kiu/lightdesk/firmware/desk-light-ctl2/desk-light-ctl2/src/tc16.c

/**
 * \file
 *
 * \brief TC16 related functionality implementation.
 (c) 2020 Microchip Technology Inc. and its subsidiaries.

    Subject to your compliance with these terms,you may use this software and
    any derivatives exclusively with Microchip products.It is your responsibility
    to comply with third party license terms applicable to your use of third party
    software (including open source software) that may accompany Microchip software.

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
    IN NO EVENT WILL MICROCHIP BE LIABLE FOR ANY INDIRECT, SPECIAL, PUNITIVE,
    INCIDENTAL OR CONSEQUENTIAL LOSS, DAMAGE, COST OR EXPENSE OF ANY KIND
    WHATSOEVER RELATED TO THE SOFTWARE, HOWEVER CAUSED, EVEN IF MICROCHIP HAS
    BEEN ADVISED OF THE POSSIBILITY OR THE DAMAGES ARE FORESEEABLE. TO THE
    FULLEST EXTENT ALLOWED BY LAW, MICROCHIP'S TOTAL LIABILITY ON ALL CLAIMS IN
    ANY WAY RELATED TO THIS SOFTWARE WILL NOT EXCEED THE AMOUNT OF FEES, IF ANY,
    THAT YOU HAVE PAID DIRECTLY TO MICROCHIP FOR THIS SOFTWARE.
 */

/**
 * \addtogroup doc_driver_tc16
 *
 * \section doc_driver_tc16_rev Revision History
 * - v0.0.0.1 Initial Commit
 *
 *@{
 */
#include <tc16.h>
#include <utils.h>

/**
 * \brief Initialize TIMER_1 interface
 *
 * \return Initialization status.
 */
int8_t TIMER_1_init()
{

	/* Enable TC1 */
	PRR0 &= ~(1 << PRTIM1);

	// TCCR1A = (0 << COM1A1) | (0 << COM1A0) /* Normal port operation, OCA disconnected */
	//		 | (0 << COM1B1) | (0 << COM1B0) /* Normal port operation, OCB disconnected */
	//		 | (0 << WGM11) | (0 << WGM10); /* TC16 Mode 12 CTC */

	TCCR1B = (1 << WGM13) | (1 << WGM12)                /* TC16 Mode 12 CTC */
	         | 0 << ICNC1                               /* Input Capture Noise Canceler: disabled */
	         | 0 << ICES1                               /* Input Capture Edge Select: disabled */
	         | (1 << CS12) | (0 << CS11) | (1 << CS10); /* IO clock divided by 1024 */

	ICR1 = 0x1000; /* Top counter value: 0x1000 */

	OCR1A = 0x1000; /* Output compare A: 0x1000 */

	// OCR1B = 0x0; /* Output compare B: 0x0 */

	// GTCCR = 0 << TSM /* Timer/Counter Synchronization Mode: disabled */
	//		 | 0 << PSRASY /* Prescaler Reset Timer/Counter2: disabled */
	//		 | 0 << PSRSYNC; /* Prescaler Reset: disabled */

	TIMSK1 = 0 << OCIE1B   /* Output Compare B Match Interrupt Enable: disabled */
	         | 1 << OCIE1A /* Output Compare A Match Interrupt Enable: enabled */
	         | 0 << ICIE1  /* Input Capture Interrupt Enable: disabled */
	         | 0 << TOIE1; /* Overflow Interrupt Enable: disabled */

	return 0;
}

/**
 * \brief Initialize TIMER_2 interface
 *
 * \return Initialization status.
 */
int8_t TIMER_2_init()
{

	/* Enable TC3 */
	PRR1 &= ~(1 << PRTIM3);

	// TCCR3A = (0 << COM3A1) | (0 << COM3A0) /* Normal port operation, OCA disconnected */
	//		 | (0 << COM3B1) | (0 << COM3B0) /* Normal port operation, OCB disconnected */
	//		 | (0 << WGM31) | (0 << WGM30); /* TC16 Mode 12 CTC */

	TCCR3B = (1 << WGM33) | (1 << WGM32)                /* TC16 Mode 12 CTC */
	         | 0 << ICNC3                               /* Input Capture Noise Canceler: disabled */
	         | 0 << ICES3                               /* Input Capture Edge Select: disabled */
	         | (1 << CS32) | (0 << CS31) | (0 << CS30); /* IO clock divided by 256 */

	ICR3 = 0x1; /* Top counter value: 0x1 */

	OCR3A = 0x1; /* Output compare A: 0x1 */

	// OCR3B = 0x0; /* Output compare B: 0x0 */

	// GTCCR = 0 << TSM /* Timer/Counter Synchronization Mode: disabled */
	//		 | 0 << PSRASY /* Prescaler Reset Timer/Counter2: disabled */
	//		 | 0 << PSRSYNC; /* Prescaler Reset: disabled */

	TIMSK3 = 0 << OCIE3B   /* Output Compare B Match Interrupt Enable: disabled */
	         | 1 << OCIE3A /* Output Compare A Match Interrupt Enable: enabled */
	         | 0 << ICIE3  /* Input Capture Interrupt Enable: disabled */
	         | 0 << TOIE3; /* Overflow Interrupt Enable: disabled */

	return 0;
}
